Albinjm72/Microchip-ATSAME54-Development-Board/assets/Layout_1.png

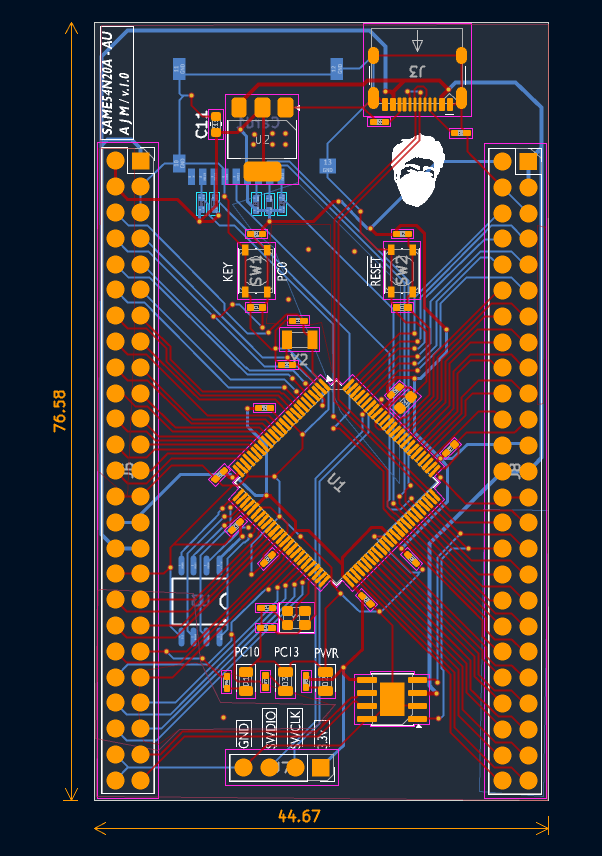
assets/Layout_1.png
