Albinjm72/Microchip-ATSAME54-Development-Board/assets/Layout_2.png

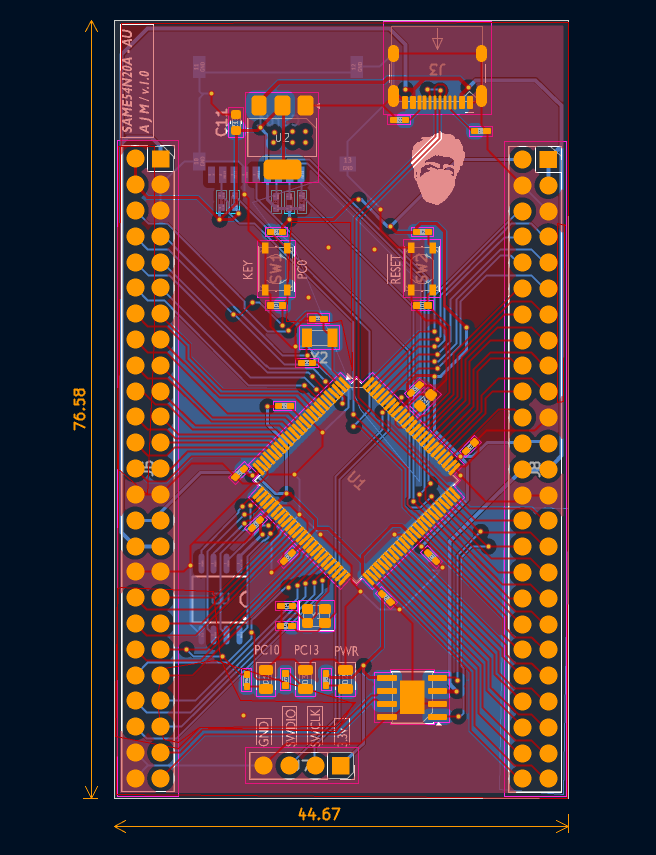
assets/Layout_2.png
