Albinjm72/Microchip-ATSAME54-Development-Board/assets/Layout_3.png

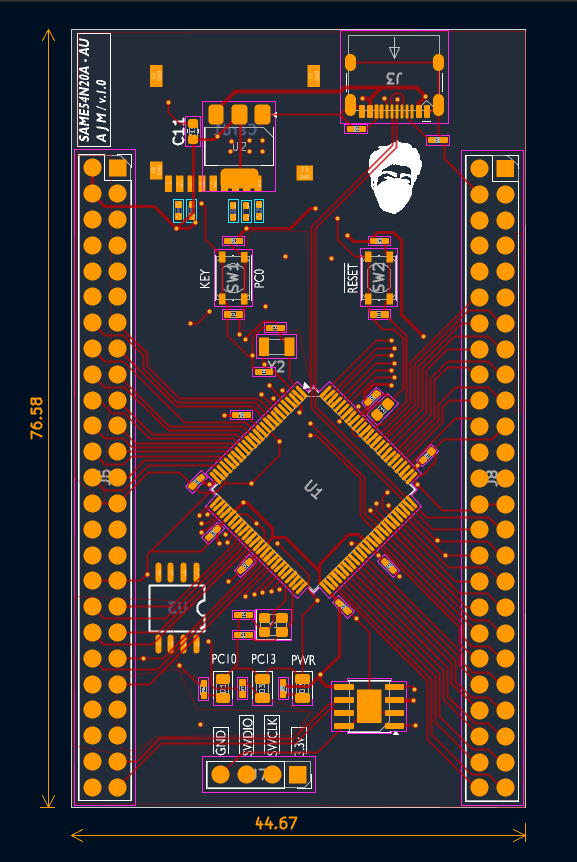
assets/Layout_3.png
