Albinjm72/Microchip-ATSAME54-Development-Board/assets/Layout_Bottom.png

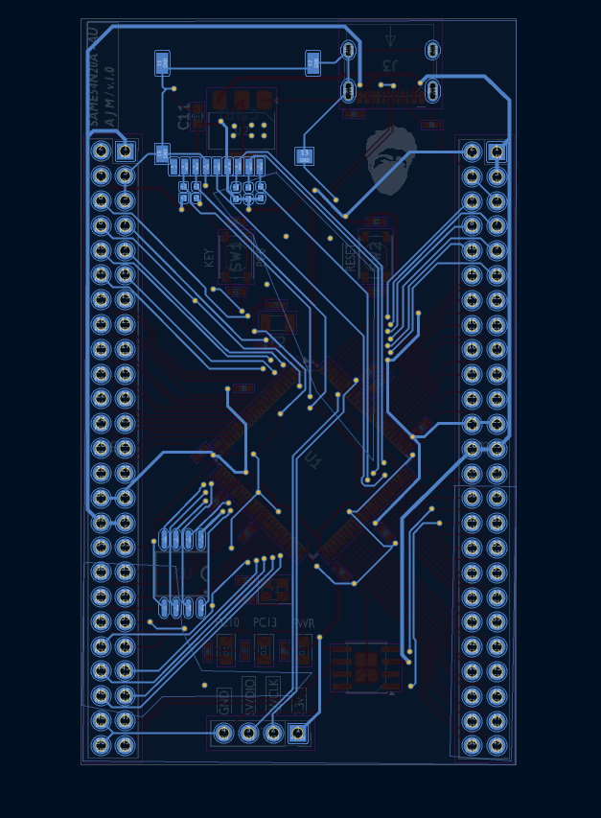
assets/Layout_Bottom.png
